richteel/Psion-Organiser-II---Graphic-LCD/Code/sketch_April_Fools/logo.h

#define Psion_logo_122x32_20bw_width 122
#define Psion_logo_122x32_20bw_height 32
static unsigned char Psion_logo_122x32_20bw_bits[] U8X8_PROGMEM = {
   0x00, 0x00, 0x00, 0x00, 0x00, 0x00, 0x00, 0x00, 0x00, 0x00, 0x00, 0x00,
   0x00, 0x00, 0x00, 0x00, 0x00, 0x00, 0x00, 0xf8, 0xff, 0xfd, 0x7f, 0xff,
   0xfd, 0xff, 0xfe, 0x3f, 0x00, 0x00, 0x00, 0x00, 0x00, 0x00, 0x00, 0xf8,
   0xff, 0xfd, 0x7f, 0xff, 0xfd, 0xff, 0xfe, 0x3f, 0x00, 0x00, 0x00, 0x00,
   0x00, 0x00, 0x00, 0x78, 0xef, 0xfd, 0x7f, 0xff, 0xfd, 0xff, 0x06, 0x3c,
   0x00, 0x00, 0x00, 0x00, 0x00, 0x00, 0x00, 0x78, 0xef, 0x9d, 0x73, 0xff,
   0x8d, 0x8f, 0x1e, 0x30, 0x00, 0x00, 0x00, 0x00, 0x00, 0x00, 0x00, 0x78,
   0xe6, 0x0d, 0x61, 0xff, 0x0d, 0x87, 0xfe, 0x3f, 0x00, 0x00, 0x00, 0x00,
   0x00, 0x00, 0x00, 0xf8, 0xf0, 0xed, 0x6f, 0x83, 0x7d, 0xf2, 0x06, 0x20,
   0x00, 0x00, 0x00, 0x00, 0x00, 0x00, 0x00, 0xf8, 0xff, 0xed, 0x6f, 0xff,
   0x7d, 0xf2, 0xfe, 0x3f, 0x00, 0x00, 0x00, 0x00, 0x00, 0x00, 0x00, 0x18,
   0x80, 0x0d, 0x61, 0x83, 0x0d, 0x87, 0x06, 0x20, 0x00, 0x00, 0x00, 0x00,
   0x00, 0x00, 0x00, 0x18, 0x80, 0x9d, 0x73, 0x83, 0x8d, 0x8f, 0x06, 0x20,
   0x00, 0x00, 0x00, 0x00, 0x00, 0x00, 0x00, 0xf8, 0xff, 0xfd, 0x7f, 0xff,
   0xfd, 0xff, 0xfe, 0x3f, 0x00, 0x00, 0x00, 0x00, 0x00, 0x00, 0x00, 0xf8,
   0xff, 0xfd, 0x7f, 0xff, 0xfd, 0xff, 0xfe, 0x3f, 0x00, 0x00, 0x00, 0x00,
   0x00, 0x00, 0x00, 0xf8, 0xff, 0xfd, 0x7f, 0xff, 0xfd, 0xff, 0xfe, 0x3f,
   0x00, 0x00, 0x00, 0x00, 0x00, 0x00, 0x00, 0xf8, 0xff, 0xfd, 0x7f, 0xff,
   0xfd, 0xff, 0xfe, 0x3f, 0x00, 0x00, 0x00, 0x00, 0x00, 0x00, 0x00, 0xf8,
   0xff, 0xfd, 0x7f, 0xff, 0xfd, 0xff, 0xfe, 0x3f, 0x00, 0x00, 0x00, 0x00,
   0x00, 0x00, 0x00, 0x38, 0xf0, 0x3d, 0x78, 0xc7, 0x7d, 0xf8, 0x8e, 0x33,
   0x00, 0x00, 0x00, 0x00, 0x00, 0x00, 0x00, 0x38, 0xe0, 0x1d, 0x70, 0xc7,
   0x3d, 0xf0, 0x8e, 0x33, 0x00, 0x00, 0x00, 0x00, 0x00, 0x00, 0x00, 0x38,
   0xc6, 0x1d, 0x73, 0xc7, 0x1d, 0xe3, 0x0e, 0x33, 0x00, 0x00, 0x00, 0x00,
   0x00, 0x00, 0x00, 0x38, 0xc6, 0x1d, 0x7f, 0xc7, 0x1d, 0xe3, 0x0e, 0x33,
   0x00, 0x00, 0x00, 0x00, 0x00, 0x00, 0x00, 0x38, 0xc6, 0x1d, 0x7e, 0xc7,
   0x1d, 0xe3, 0x0e, 0x32, 0x00, 0x00, 0x00, 0x00, 0x00, 0x00, 0x00, 0x38,
   0xe0, 0x3d, 0x7c, 0xc7, 0x1d, 0xe3, 0x0e, 0x32, 0x00, 0x00, 0x00, 0x00,
   0x00, 0x00, 0x00, 0x38, 0xf0, 0xfd, 0x78, 0xc7, 0x1d, 0xe3, 0x4e, 0x32,
   0x00, 0x00, 0x00, 0x00, 0x00, 0x00, 0x00, 0x38, 0xfe, 0xfd, 0x71, 0xc7,
   0x1d, 0xe3, 0x4e, 0x30, 0x00, 0x00, 0x00, 0x00, 0x00, 0x00, 0x00, 0x38,
   0xfe, 0xfd, 0x73, 0xc7, 0x1d, 0xe3, 0xce, 0x30, 0x00, 0x00, 0x00, 0x00,
   0x00, 0x00, 0x00, 0x38, 0xfe, 0x1d, 0x73, 0xc7, 0x1d, 0xe3, 0xce, 0x30,
   0x00, 0x00, 0x00, 0x00, 0x00, 0x00, 0x00, 0x38, 0xfe, 0x1d, 0x70, 0xc7,
   0x3d, 0xf0, 0xce, 0x31, 0x00, 0x00, 0x00, 0x00, 0x00, 0x00, 0x00, 0x38,
   0xfe, 0x3d, 0x78, 0xc7, 0x7d, 0xf8, 0xce, 0x31, 0x00, 0x00, 0x00, 0x00,
   0x00, 0x00, 0x00, 0xf8, 0xff, 0xfd, 0x7f, 0xff, 0xfd, 0xff, 0xfe, 0x3f,
   0x00, 0x00, 0x00, 0x00, 0x00, 0x00, 0x00, 0xf8, 0xff, 0xfd, 0x7f, 0xff,
   0xfd, 0xff, 0xfe, 0x3f, 0x00, 0x00, 0x00, 0x00, 0x00, 0x00, 0x00, 0xf8,
   0xff, 0xfd, 0x7f, 0xff, 0xfd, 0xff, 0xfe, 0x3f, 0x00, 0x00, 0x00, 0x00,
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
