richteel/Psion-Organiser-II---Graphic-LCD/Code/sketch_April_Fools/menu.h

#define Menu_width 122
#define Menu_height 32
static unsigned char Menu_bits[] U8X8_PROGMEM = {
   0x00, 0x00, 0x00, 0x00, 0x00, 0x00, 0x00, 0x00, 0x00, 0x00, 0x00, 0x00,
   0x00, 0x00, 0x00, 0x00, 0xc0, 0xff, 0xff, 0xff, 0xff, 0x00, 0x00, 0x00,
   0x00, 0x00, 0x00, 0x00, 0x00, 0x00, 0x00, 0x00, 0xc0, 0xff, 0xff, 0xff,
   0xff, 0x00, 0x00, 0x00, 0x00, 0x00, 0x00, 0x00, 0x00, 0x00, 0x00, 0x00,
   0xc0, 0xff, 0xff, 0xff, 0xff, 0x00, 0x80, 0x00, 0x00, 0x00, 0x00, 0x00,
   0x00, 0x00, 0x00, 0x00, 0xc0, 0x7f, 0x80, 0xff, 0xff, 0x00, 0x80, 0x80,
   0x20, 0x00, 0x00, 0x00, 0x38, 0x00, 0x00, 0x00, 0xc0, 0x7f, 0xbf, 0xff,
   0xff, 0x00, 0x80, 0x00, 0x11, 0x00, 0x00, 0x00, 0xc6, 0x00, 0x00, 0x00,
   0xc0, 0x7f, 0xb1, 0xff, 0xff, 0x00, 0xf0, 0x07, 0x0a, 0x00, 0x00, 0x00,
   0x11, 0x01, 0x00, 0x00, 0xc0, 0x7f, 0xbf, 0xff, 0xff, 0x00, 0x80, 0x00,
   0x04, 0x00, 0x00, 0x80, 0x10, 0x02, 0x00, 0x00, 0xc0, 0x7f, 0x15, 0xe0,
   0xff, 0x00, 0x80, 0x00, 0x0a, 0x00, 0x00, 0x80, 0x10, 0x02, 0x00, 0x00,
   0xc0, 0x7f, 0xdf, 0xef, 0xff, 0x00, 0x80, 0x00, 0x11, 0x00, 0x00, 0x40,
   0x10, 0x04, 0x00, 0x00, 0xc0, 0x7f, 0x59, 0xe9, 0xff, 0x00, 0x00, 0x80,
   0x20, 0x00, 0x00, 0x40, 0x10, 0x04, 0x00, 0x00, 0xc0, 0x7f, 0xdf, 0xef,
   0xff, 0x00, 0x00, 0x00, 0x00, 0x00, 0x00, 0x40, 0x20, 0x04, 0x00, 0x00,
   0xc0, 0x7f, 0x5f, 0xec, 0xff, 0x00, 0x00, 0x08, 0x00, 0x00, 0x00, 0x80,
   0x40, 0x02, 0x00, 0x00, 0xc0, 0x7f, 0xc0, 0xef, 0xff, 0x00, 0x00, 0x04,
   0x00, 0x00, 0x00, 0x80, 0x00, 0x02, 0x00, 0x00, 0xc0, 0xff, 0x5f, 0xe8,
   0xff, 0x00, 0x00, 0x02, 0x00, 0x00, 0x00, 0x00, 0x01, 0x01, 0x00, 0x00,
   0xc0, 0xff, 0xdf, 0xef, 0xff, 0x00, 0x00, 0x81, 0x3f, 0x00, 0x00, 0x00,
   0xc6, 0x00, 0x00, 0x00, 0xc0, 0xff, 0xdf, 0xef, 0xff, 0x00, 0x80, 0x00,
   0x00, 0x00, 0x00, 0x00, 0x38, 0x00, 0x00, 0x00, 0xc0, 0xff, 0x1f, 0xe0,
   0xff, 0x00, 0x40, 0x00, 0x00, 0x00, 0x00, 0x00, 0x00, 0x00, 0x00, 0x00,
   0xc0, 0xff, 0xff, 0xff, 0xff, 0x00, 0x20, 0x00, 0x00, 0x00, 0x00, 0x00,
   0x00, 0x00, 0x00, 0x00, 0xc0, 0xff, 0xff, 0xff, 0xff, 0x00, 0x00, 0x00,
   0x00, 0x00, 0x00, 0x00, 0x00, 0x00, 0x00, 0x00, 0xc0, 0xff, 0xff, 0xff,
   0xff, 0x00, 0x00, 0x00, 0x00, 0x00, 0x00, 0x00, 0x00, 0x00, 0x00, 0x00,
   0xc0, 0xc1, 0xc7, 0xc0, 0xf8, 0x00, 0x1e, 0x8e, 0x01, 0x0f, 0x80, 0xdf,
   0x8e, 0xfb, 0x01, 0x00, 0xc0, 0x99, 0xc7, 0xf3, 0xf8, 0x00, 0x33, 0x8e,
   0x81, 0x19, 0x00, 0xc6, 0x8e, 0x1b, 0x00, 0x00, 0xc0, 0x39, 0x93, 0x73,
   0xf2, 0x80, 0x01, 0x9b, 0xc1, 0x00, 0x00, 0xc6, 0xde, 0x1b, 0x00, 0x00,
   0xc0, 0x39, 0x93, 0x73, 0xf2, 0x80, 0x01, 0x9b, 0xc1, 0x00, 0x00, 0xc6,
   0xde, 0x1b, 0x00, 0x00, 0xc0, 0x39, 0x93, 0x73, 0xf2, 0x80, 0x01, 0x9b,
   0xc1, 0x00, 0x00, 0xc6, 0x56, 0xfb, 0x01, 0x00, 0xc0, 0x39, 0x93, 0x73,
   0xf2, 0x80, 0x01, 0x9b, 0xc1, 0x00, 0x00, 0xc6, 0x56, 0x1b, 0x00, 0x00,
   0xc0, 0x39, 0x01, 0x33, 0xe0, 0x80, 0x81, 0xbf, 0xc1, 0x00, 0x00, 0xc6,
   0x76, 0x1b, 0x00, 0x00, 0xc0, 0x99, 0x39, 0x33, 0xe7, 0x00, 0xb3, 0xb1,
   0x81, 0x19, 0x00, 0xc6, 0x76, 0x1b, 0x00, 0x00, 0xc0, 0xc1, 0x39, 0x33,
   0xe7, 0x00, 0x9e, 0xb1, 0x1f, 0x0f, 0x00, 0xc6, 0x26, 0xfb, 0x01, 0x00,
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
